sudhi345/Measurement-Of-Capacity-Of-A-Battery/gallery/pcb_soldered.jpg

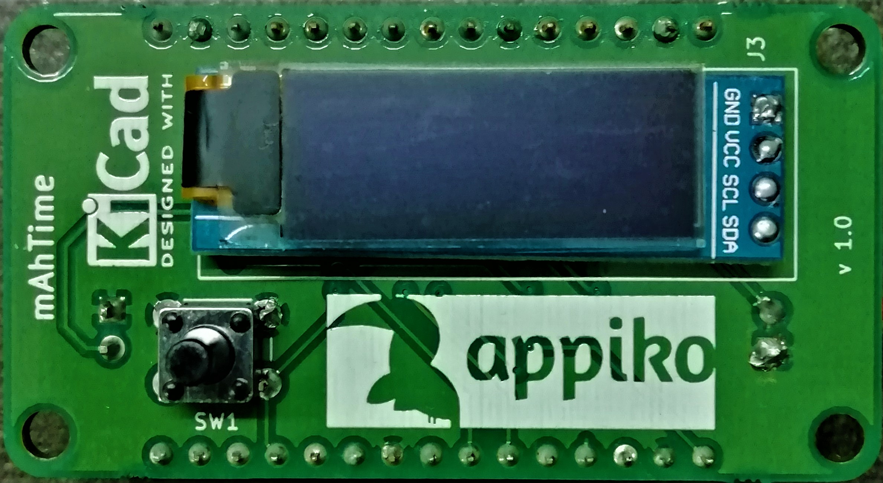
gallery/pcb_soldered.jpg
