sudhi345/Measurement-Of-Capacity-Of-A-Battery/PCB_KiCAD/PDF/CapacityOfBattery-Cmts.User.pdf

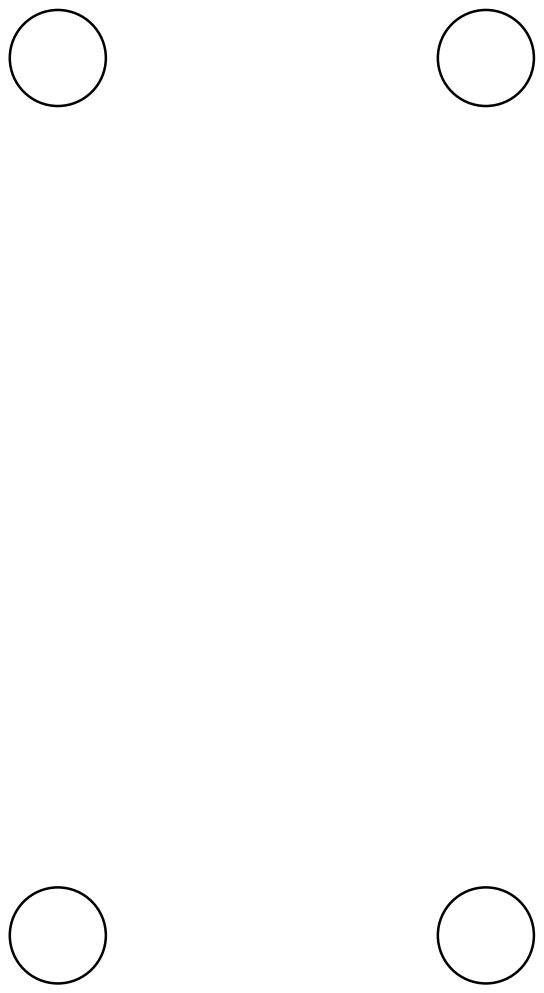
[picture p18: page 1]
