sudhi345/Measurement-Of-Capacity-Of-A-Battery/PCB_KiCAD/GBR/CapacityOfBattery-Cmts.User.pdf

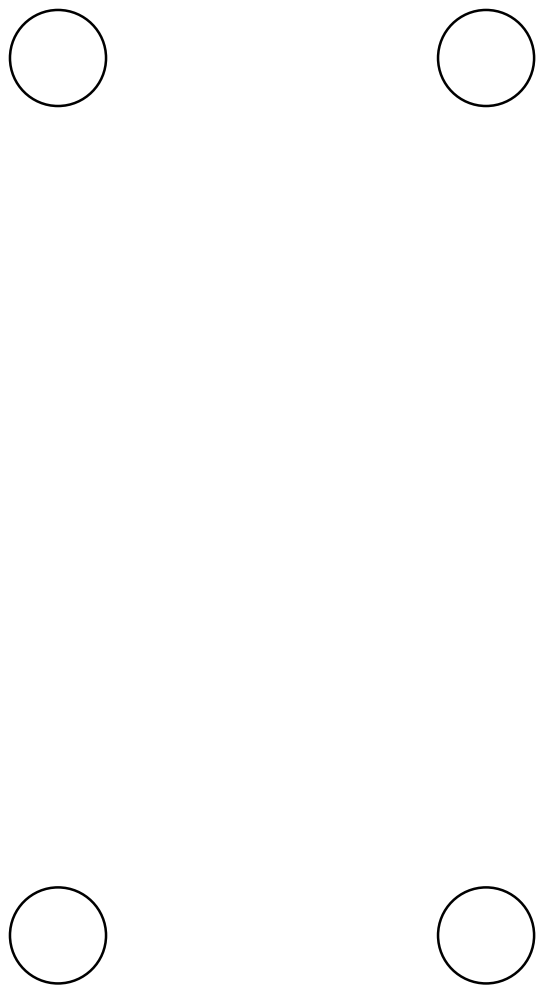
[picture p19: page 1]
